telzo2000/cool640db/img/img00002.jpg

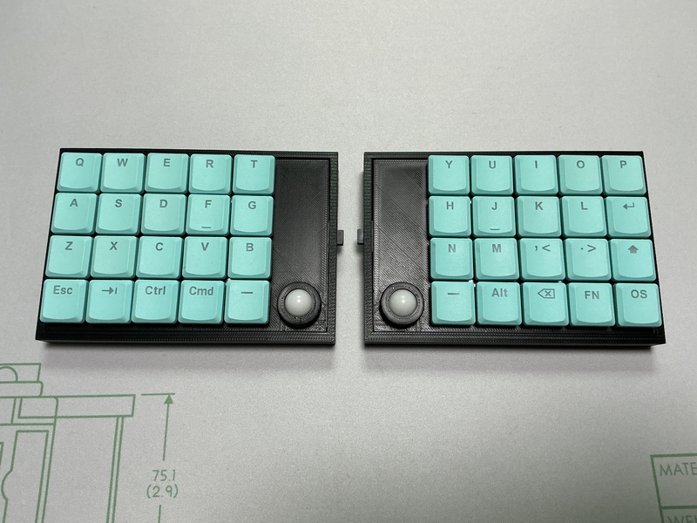
img/img00002.jpg
