telzo2000/cool640db/img/img00003.jpg

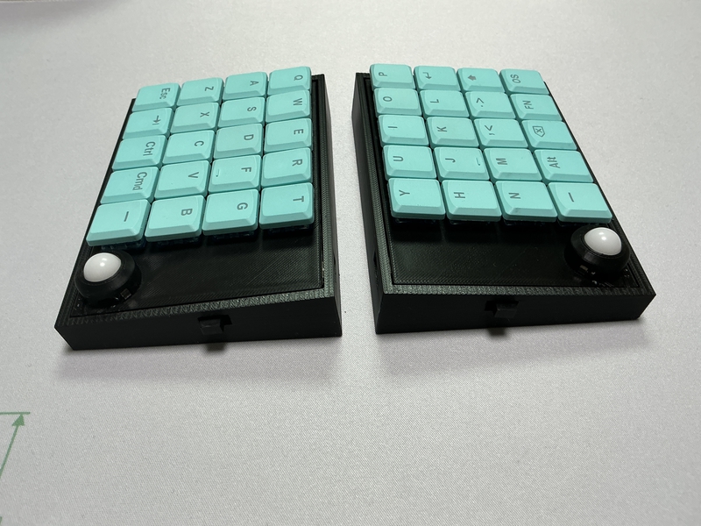
img/img00003.jpg
