telzo2000/cool640db/img/img00004.jpg

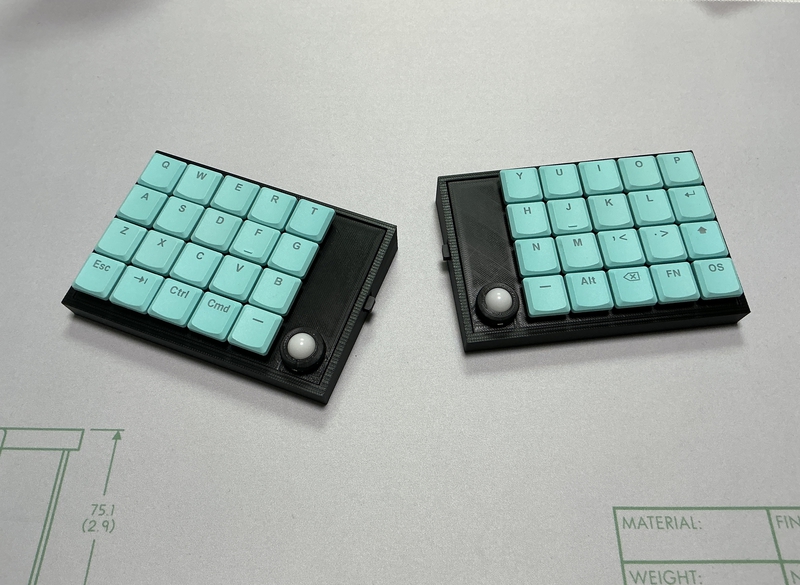
img/img00004.jpg
