telzo2000/cool640db/img/img00005.jpg

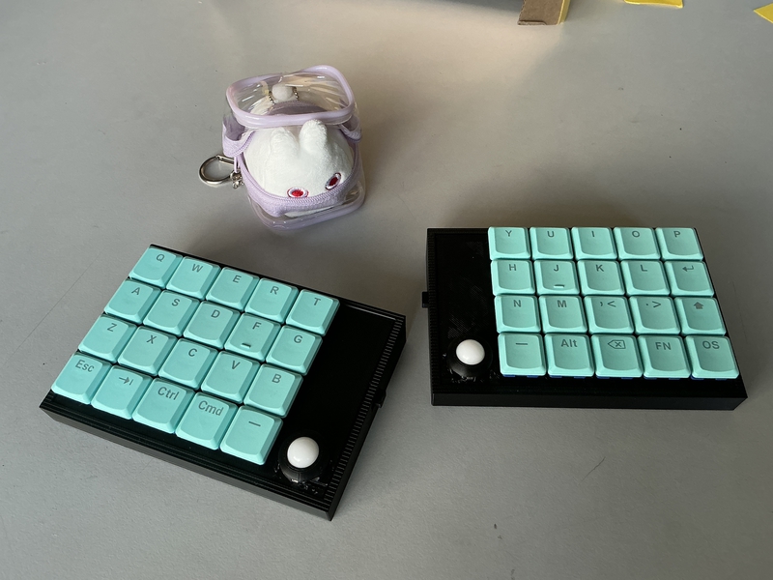
img/img00005.jpg
