telzo2000/cool640db/img/img00009.jpg

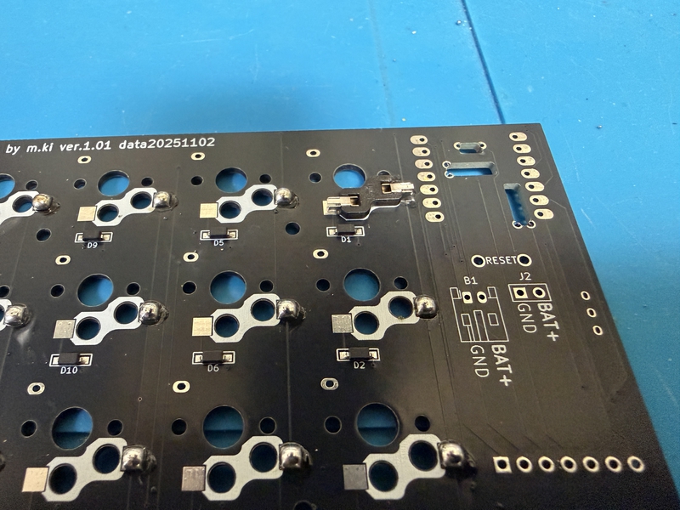
img/img00009.jpg
