telzo2000/cool640db/img/img00011.jpg

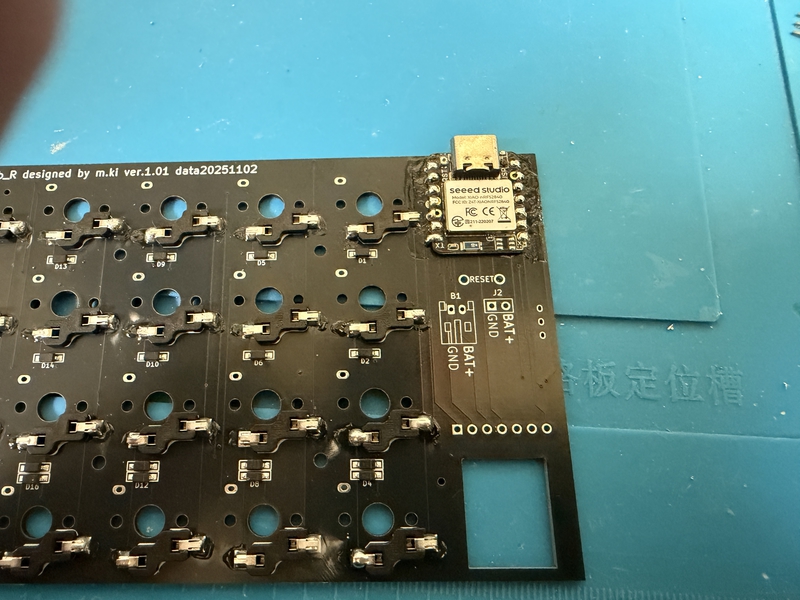
img/img00011.jpg
